pike00/fi-collar-charger-plate/images/plate-front.png

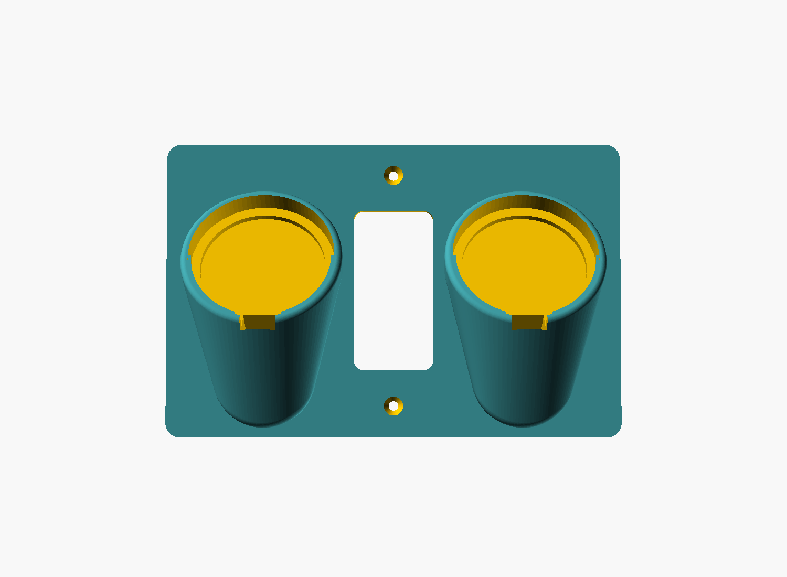
images/plate-front.png
