pike00/fi-collar-charger-plate/images/plate-side.png

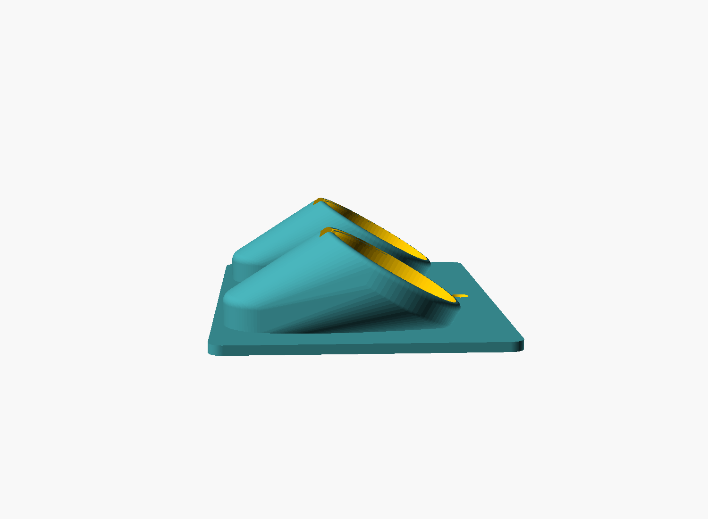
images/plate-side.png
